jostsalathe/75PercentMoreSalad/pcb/75PercentMoreSalad/75PercentMoreSalad.kicad_sch

## KiCad design pcb/75PercentMoreSalad/75PercentMoreSalad.kicad_sch (2022-12-12, an earlier design)

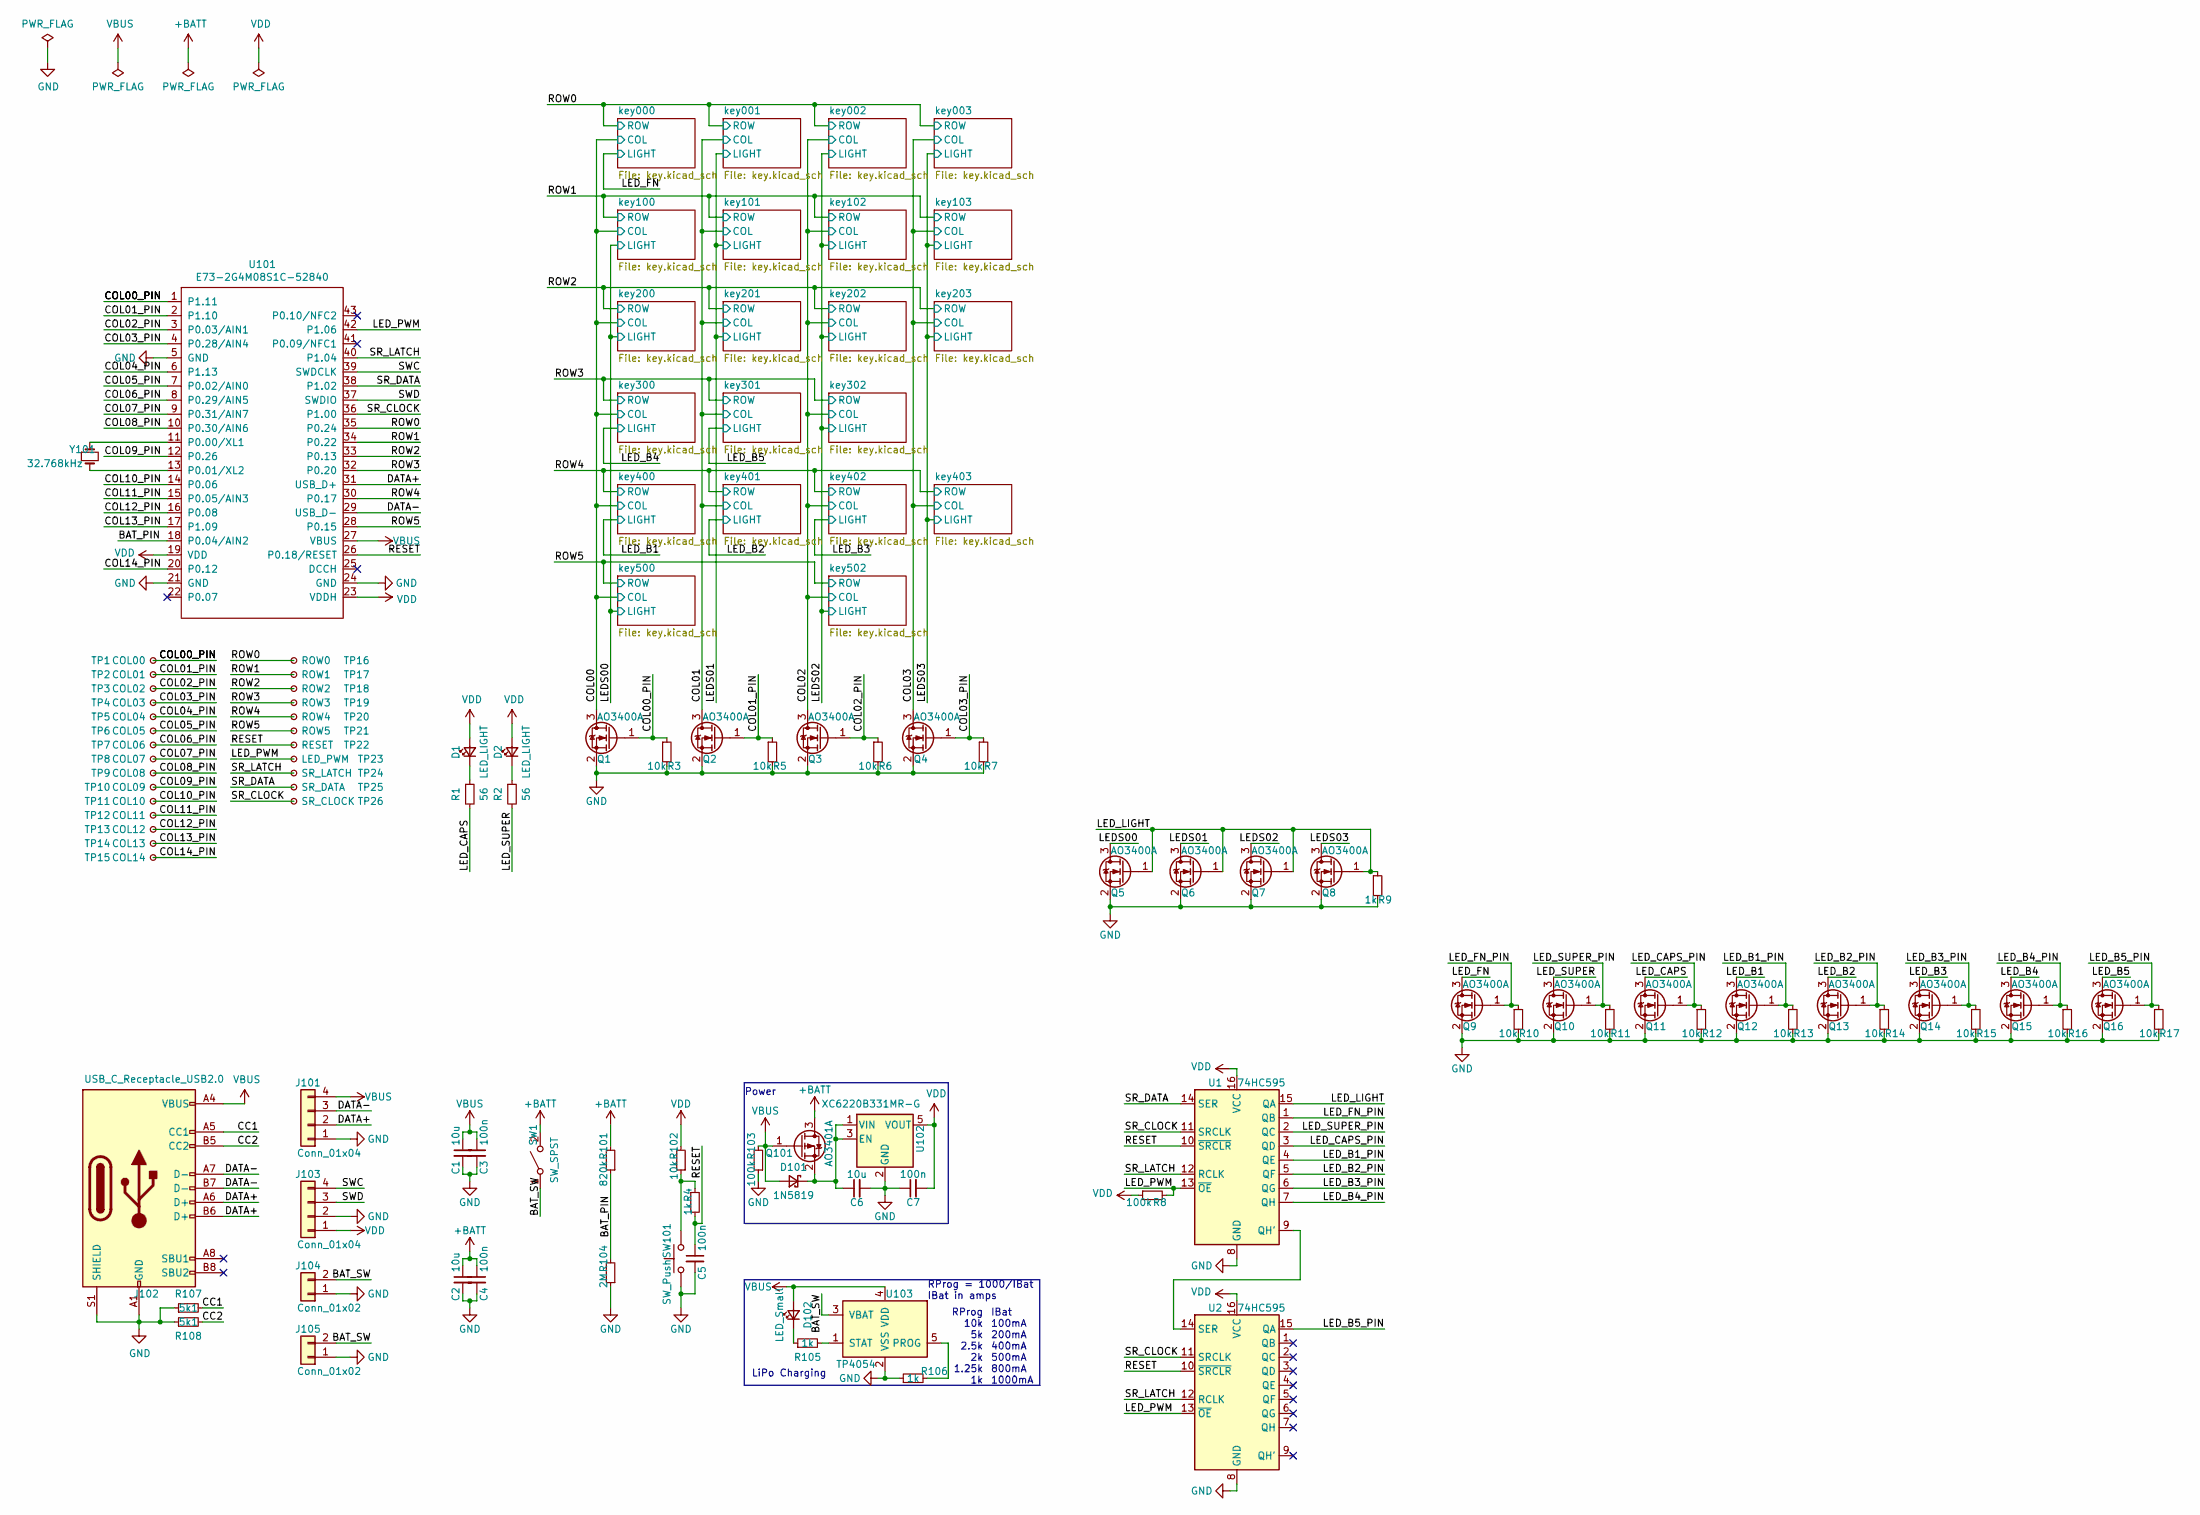
[picture p14: schematic 75PercentMoreSalad.kicad_sch]

Parts:
C1, C2, C6: 10u; C_0805_2012Metric
C3, C4, C5, C7: 100n; C_0805_2012Metric
D1, D2: LED_LIGHT
D101: 1N5819; D_SOD-323F
D102: LED_Small
J101: Conn_01x04; connector_usb
J102: USB_C_Receptacle_USB2.0; USB-C_C168688
J103: Conn_01x04; connector_swd
J104, J105: Conn_01x02; PinHeader_1x02_P2.54mm_Vertical
Q1, Q2, Q3, Q4, Q5, Q6, Q7, Q8, Q9, Q10, Q11, Q12, Q13, Q14, Q15, Q16: AO3400A; SOT-23
Q101: AO3401A; SOT-23
R1, R2: 56; R_0805_2012Metric
R3, R5, R6, R7, R10, R11, R12, R13, R14, R15, R16, R17, R102: 10k
R4, R9, R105, R106: 1k
R8, R103: 100k
R101: 820k
R104: 2M
R107, R108: 5k1
SW1: SW_SPST
SW101: SW_Push
TP1: COL00; TestPoint_Pad_D1.0mm
TP2: COL01; TestPoint_Pad_D1.0mm
TP3: COL02; TestPoint_Pad_D1.0mm
TP4: COL03; TestPoint_Pad_D1.0mm
TP5: COL04; TestPoint_Pad_D1.0mm
TP6: COL05; TestPoint_Pad_D1.0mm
TP7: COL06; TestPoint_Pad_D1.0mm
TP8: COL07; TestPoint_Pad_D1.0mm
TP9: COL08; TestPoint_Pad_D1.0mm
TP10: COL09; TestPoint_Pad_D1.0mm
TP11: COL10; TestPoint_Pad_D1.0mm
TP12: COL11; TestPoint_Pad_D1.0mm
TP13: COL12; TestPoint_Pad_D1.0mm
TP14: COL13; TestPoint_Pad_D1.0mm
TP15: COL14; TestPoint_Pad_D1.0mm
TP16: ROW0; TestPoint_Pad_D1.0mm
TP17: ROW1; TestPoint_Pad_D1.0mm
TP18: ROW2; TestPoint_Pad_D1.0mm
TP19: ROW3; TestPoint_Pad_D1.0mm
TP20: ROW4; TestPoint_Pad_D1.0mm
TP21: ROW5; TestPoint_Pad_D1.0mm
TP22: RESET; TestPoint_Pad_D1.0mm
TP23: LED_PWM; TestPoint_Pad_D1.0mm
TP24: SR_LATCH; TestPoint_Pad_D1.0mm
TP25: SR_DATA; TestPoint_Pad_D1.0mm
TP26: SR_CLOCK; TestPoint_Pad_D1.0mm
U1, U2: 74HC595; SOIC-16_3.9x9.9mm_P1.27mm
U101: E73-2G4M08S1C-52840
U102: XC6220B331MR-G; SOT-23-5
U103: TP4054; SOT-23-5
Y101: 32.768kHz; Crystal_SMD_MicroCrystal_CM9V-T1A-2Pin_1.6x1.0mm

Connections:
+BATT: C2.1, C4.1, Q101.3 (D), R101.2, SW1.2 (B)
BAT_PIN: R101.1, R104.2, U101.18 (P0.04/AIN2)
BAT_SW: J104.2, J105.2, SW1.1 (A), U103.3 (VBAT)
CC1: J102.A5 (CC1), R107.2
CC2: J102.B5 (CC2), R108.2
COL00: Q1.3 (D)
COL00_PIN: Q1.1 (G), R3.1, TP1.1, U101.1 (P1.11)
COL01: Q2.3 (D)
COL01_PIN: Q2.1 (G), R5.1, TP2.1, U101.2 (P1.10)
COL02: Q3.3 (D)
COL02_PIN: Q3.1 (G), R6.1, TP3.1, U101.3 (P0.03/AIN1)
COL03: Q4.3 (D)
COL03_PIN: Q4.1 (G), R7.1, TP4.1, U101.4 (P0.28/AIN4)
COL04_PIN: TP5.1, U101.6 (P1.13)
COL05_PIN: TP6.1, U101.7 (P0.02/AIN0)
COL06_PIN: TP7.1, U101.8 (P0.29/AIN5)
COL07_PIN: TP8.1, U101.9 (P0.31/AIN7)
COL08_PIN: TP9.1, U101.10 (P0.30/AIN6)
COL09_PIN: TP10.1, U101.12 (P0.26)
COL10_PIN: TP11.1, U101.14 (P0.06)
COL11_PIN: TP12.1, U101.15 (P0.05/AIN3)
COL12_PIN: TP13.1, U101.16 (P0.08)
COL13_PIN: TP14.1, U101.17 (P1.09)
COL14_PIN: TP15.1, U101.20 (P0.12)
DATA+: J101.2, J102.A6 (D+), J102.B6 (D+), U101.31 (USB_D+)
DATA-: J101.3, J102.A7 (D-), J102.B7 (D-), U101.29 (USB_D-)
GND: C1.2, C2.2, C3.2, C4.2, C5.2, C6.2, C7.1, J101.1, J102.A1 (GND), J102.A12 (GND), J102.B1 (GND), J102.B12 (GND), J102.S1 (SHIELD), J103.2, J104.1, J105.1, Q1.2 (S), Q2.2 (S), Q3.2 (S), Q4.2 (S), Q5.2 (S), Q6.2 (S), Q7.2 (S), Q8.2 (S), Q9.2 (S), Q10.2 (S), Q11.2 (S), Q12.2 (S), Q13.2 (S), Q14.2 (S), Q15.2 (S), Q16.2 (S), R3.2, R5.2, R6.2, R7.2, R9.2, R10.2, R11.2, R12.2, R13.2, R14.2, R15.2, R16.2, R17.2, R103.1, R104.1, R106.1, R107.1, R108.1, SW101.1, U1.8 (GND), U2.8 (GND), U101.5 (GND), U101.21 (GND), U101.24 (GND), U102.2 (GND), U103.2 (VSS)
LEDS00: Q5.3 (D)
LEDS01: Q6.3 (D)
LEDS02: Q7.3 (D)
LEDS03: Q8.3 (D)
LED_B1: Q12.3 (D)
LED_B1_PIN: Q12.1 (G), R13.1, U1.4 (QE)
LED_B2: Q13.3 (D)
LED_B2_PIN: Q13.1 (G), R14.1, U1.5 (QF)
LED_B3: Q14.3 (D)
LED_B3_PIN: Q14.1 (G), R15.1, U1.6 (QG)
LED_B4: Q15.3 (D)
LED_B4_PIN: Q15.1 (G), R16.1, U1.7 (QH)
LED_B5: Q16.3 (D)
LED_B5_PIN: Q16.1 (G), R17.1, U2.15 (QA)
LED_CAPS: Q11.3 (D), R1.2
LED_CAPS_PIN: Q11.1 (G), R12.1, U1.3 (QD)
LED_FN: Q9.3 (D)
LED_FN_PIN: Q9.1 (G), R10.1, U1.1 (QB)
LED_LIGHT: Q5.1 (G), Q6.1 (G), Q7.1 (G), Q8.1 (G), R9.1, U1.15 (QA)
LED_PWM: R8.2, TP23.1, U1.13 (~OE), U2.13 (~OE), U101.42 (P1.06)
LED_SUPER: Q10.3 (D), R2.2
LED_SUPER_PIN: Q10.1 (G), R11.1, U1.2 (QC)
unnamed: C6.1, D101.1 (K), Q101.2 (S), U102.1 (VIN), U102.3 (EN)
unnamed: D1.1 (K), R1.1
unnamed: D2.1 (K), R2.1
unnamed: D102.1 (K), R105.1
unnamed: R4.1, R102.1, SW101.2
unnamed: R105.2, U103.1 (STAT)
unnamed: R106.2, U103.5 (PROG)
unnamed: U1.9 (QH'), U2.14 (SER)
unnamed: U101.11 (P0.00/XL1), Y101.1
unnamed: U101.13 (P0.01/XL2), Y101.2
RESET: C5.1, R4.2, TP22.1, U1.10 (~SRCLR), U2.10 (~SRCLR), U101.26 (P0.18/RESET)
ROW0: TP16.1, U101.35 (P0.24)
ROW1: TP17.1, U101.34 (P0.22)
ROW2: TP18.1, U101.33 (P0.13)
ROW3: TP19.1, U101.32 (P0.20)
ROW4: TP20.1, U101.30 (P0.17)
ROW5: TP21.1, U101.28 (P0.15)
SR_CLOCK: TP26.1, U1.11 (SRCLK), U2.11 (SRCLK), U101.36 (P1.00)
SR_DATA: TP25.1, U1.14 (SER), U101.38 (P1.02)
SR_LATCH: TP24.1, U1.12 (RCLK), U2.12 (RCLK), U101.40 (P1.04)
SWC: J103.4, U101.39 (SWDCLK)
SWD: J103.3, U101.37 (SWDIO)
VBUS: C1.1, C3.1, D101.2 (A), D102.2 (A), J101.4, J102.A4 (VBUS), J102.A9 (VBUS), J102.B4 (VBUS), J102.B9 (VBUS), Q101.1 (G), R103.2, U101.27 (VBUS), U103.4 (VDD)
VDD: C7.2, D1.2 (A), D2.2 (A), J103.1, R8.1, R102.2, U1.16 (VCC), U2.16 (VCC), U101.19 (VDD), U101.23 (VDDH), U102.5 (VOUT)

Notes on the sheet:
RProg = 1000/IBat IBat in amps
RProg 10k 5k 2.5k 2k 1.25k 1k
IBat 100mA 200mA 400mA 500mA 800mA 1000mA
LiPo Charging
Power
