jostsalathe/75PercentMoreSalad/pcb/75PercentMoreSalad/key.kicad_sch

## KiCad design pcb/75PercentMoreSalad/key.kicad_sch (2022-12-12, an earlier design)

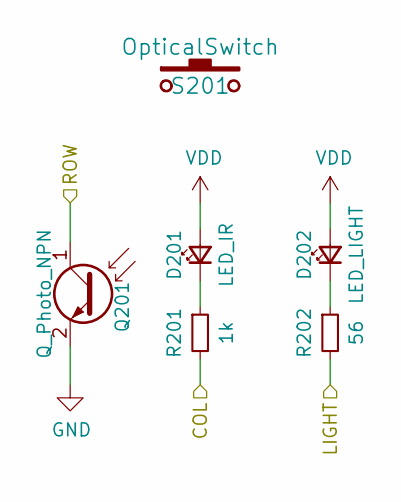
[picture p15: schematic key.kicad_sch]

Parts:
D201: LED_IR
D202: LED_LIGHT
Q201: Q_Photo_NPN
R201: 1k; R_0805_2012Metric
R202: 56; R_0805_2012Metric
S201: OpticalSwitch; KeychronLowProfileOpticalSwitch

Connections:
COL: R201.2
GND: Q201.2 (E)
LIGHT: R202.2
unnamed: D201.1 (K), R201.1
unnamed: D202.1 (K), R202.1
ROW: Q201.1 (C)
VDD: D201.2 (A), D202.2 (A)
